JuanJ-S/DAFA/Imagenes/Diagramas/Bocetado, Sistema de Tuberias.jpeg

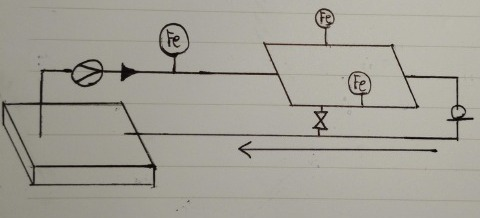
Imagenes/Diagramas/Bocetado, Sistema de Tuberias.jpeg
