JuanJ-S/DAFA/Imagenes/Diagramas/DAFA (ESP8266).png

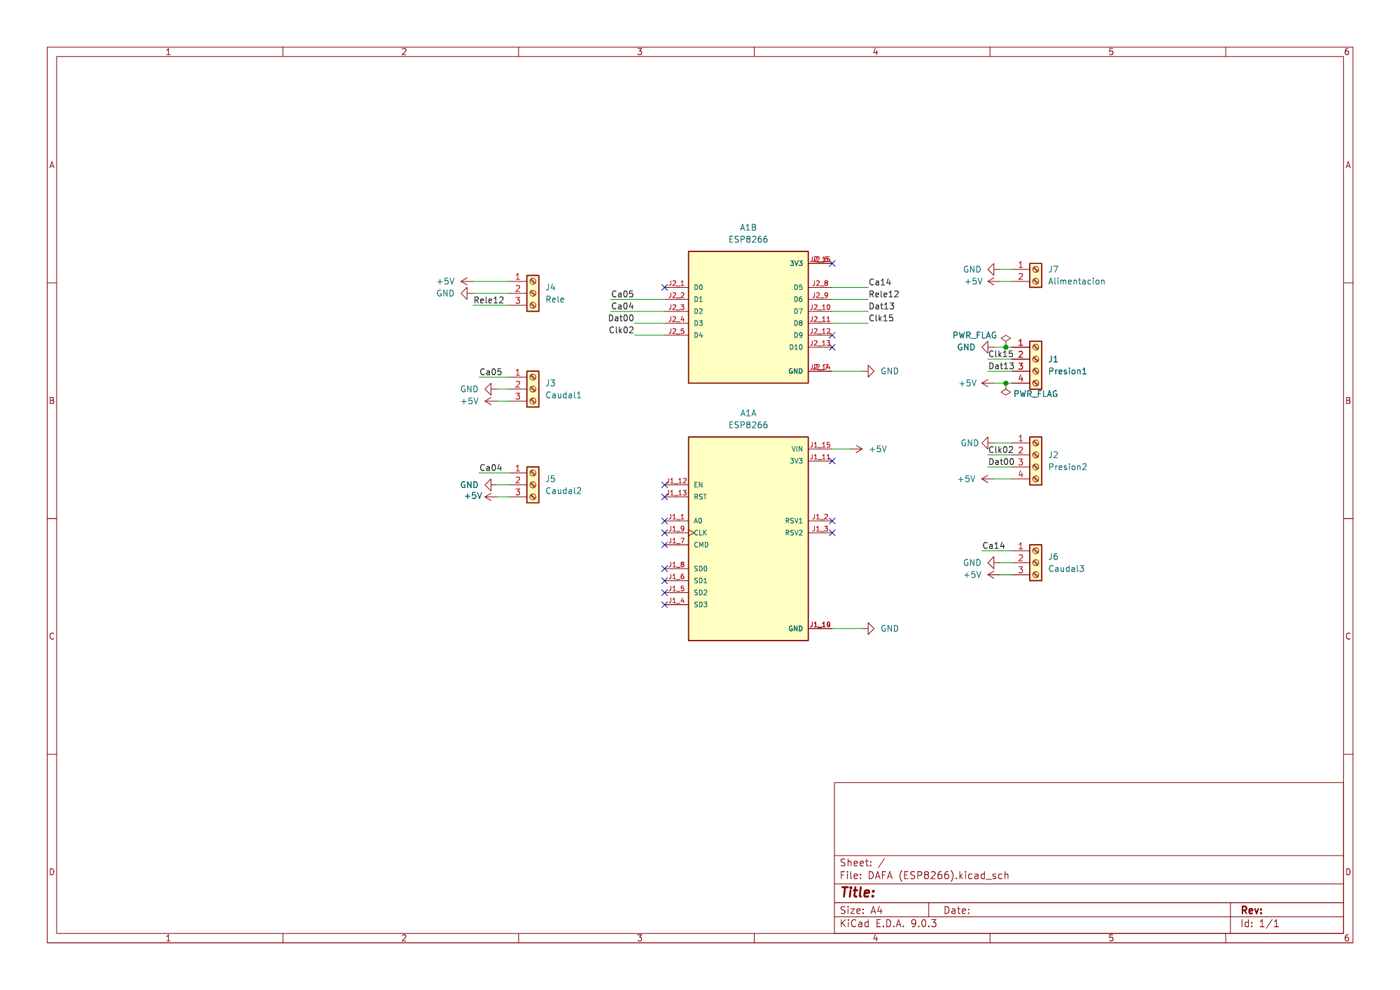
Imagenes/Diagramas/DAFA (ESP8266).png
