JuanJ-S/DAFA/Imagenes/Diagramas/Diagrama Funcionamiento.drawio.png

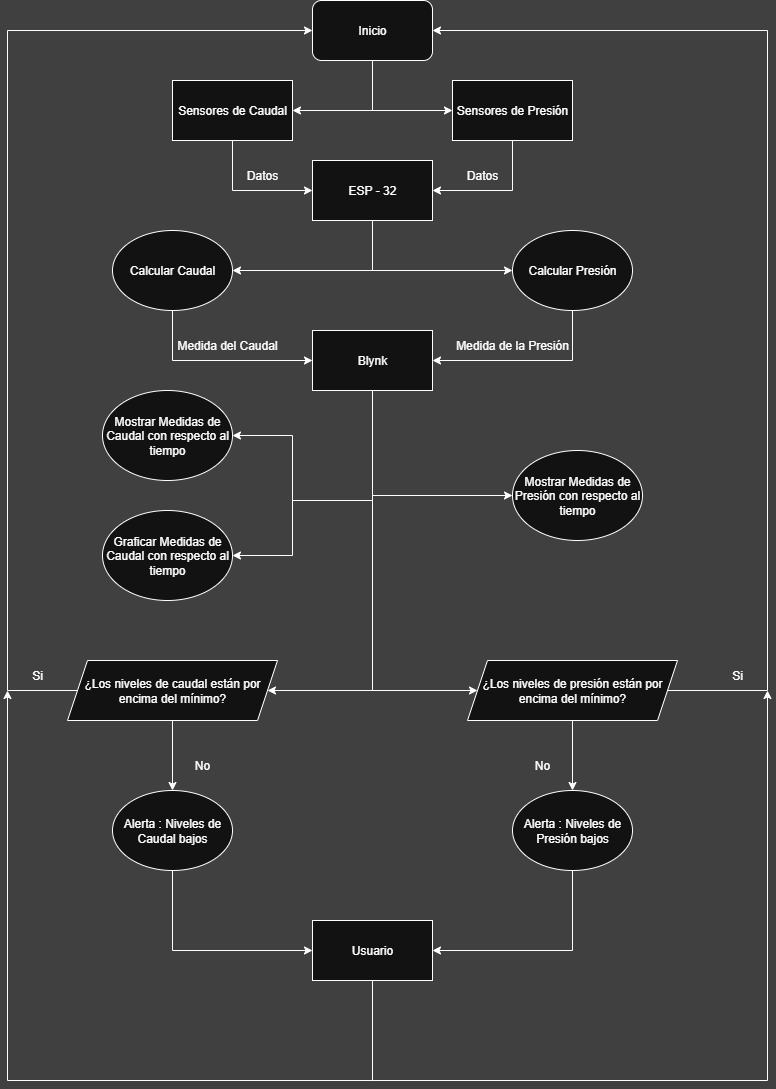
Imagenes/Diagramas/Diagrama Funcionamiento.drawio.png
