JuanJ-S/DAFA/Imagenes/Diagramas/Diagrama Tecnológico.png

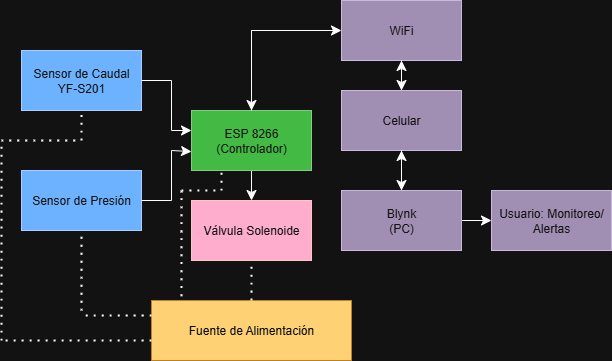
Imagenes/Diagramas/Diagrama Tecnológico.png
