JuanJ-S/DAFA/Imagenes/Diagramas/Esquema ESP32.jpeg

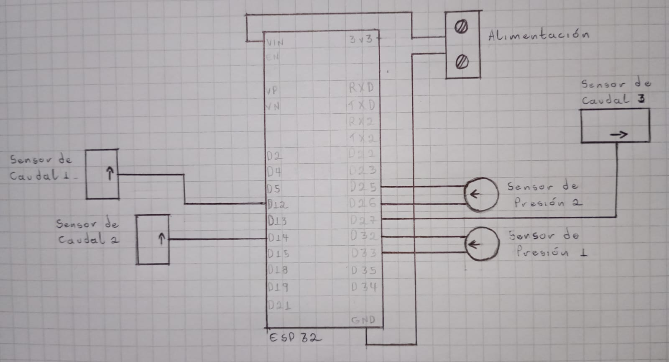
Imagenes/Diagramas/Esquema ESP32.jpeg
