JuanJ-S/DAFA/Imagenes/Diagramas/Interacción_usuario.drawio.png

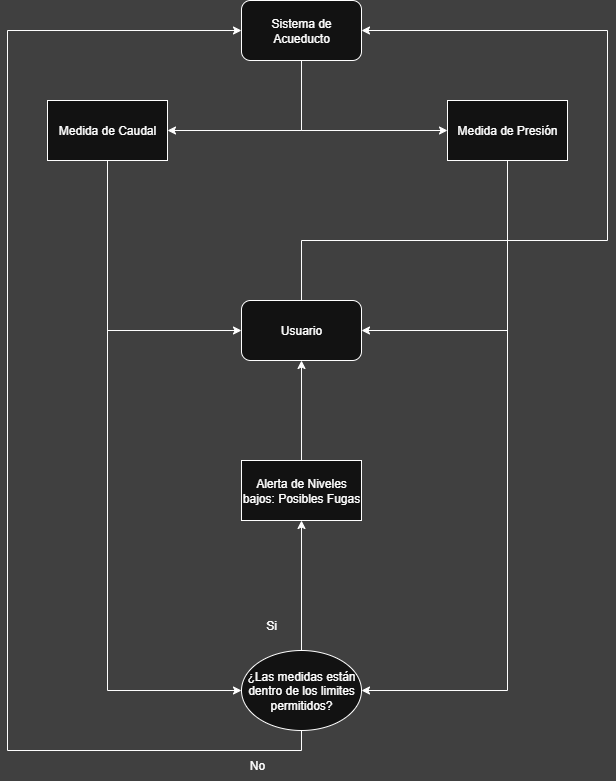
Imagenes/Diagramas/Interacción_usuario.drawio.png
