JuanJ-S/DAFA/Imagenes/Fotitos/Case - Inferior.png

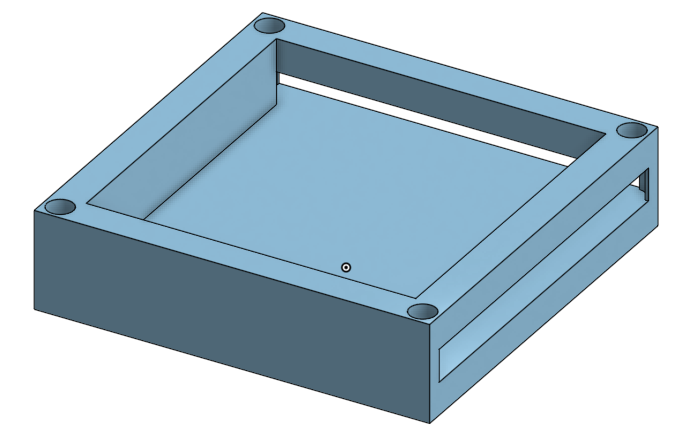
Imagenes/Fotitos/Case - Inferior.png
