JuanJ-S/DAFA/Imagenes/Fotitos/Case - Superior.png

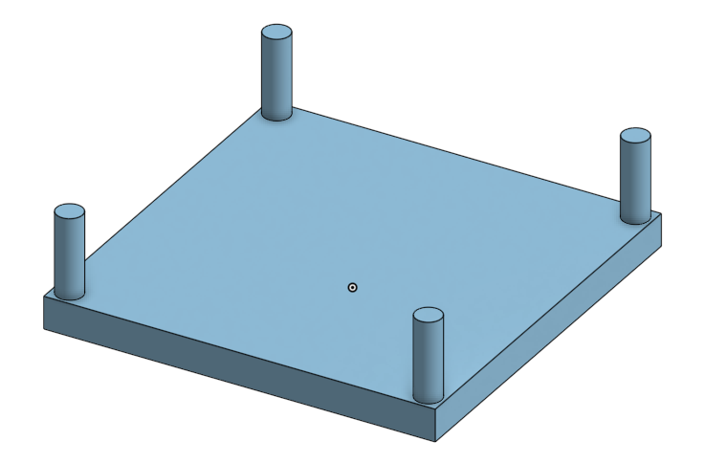
Imagenes/Fotitos/Case - Superior.png
