JuanJ-S/DAFA/Imagenes/Fotitos/Cronograma.jpg

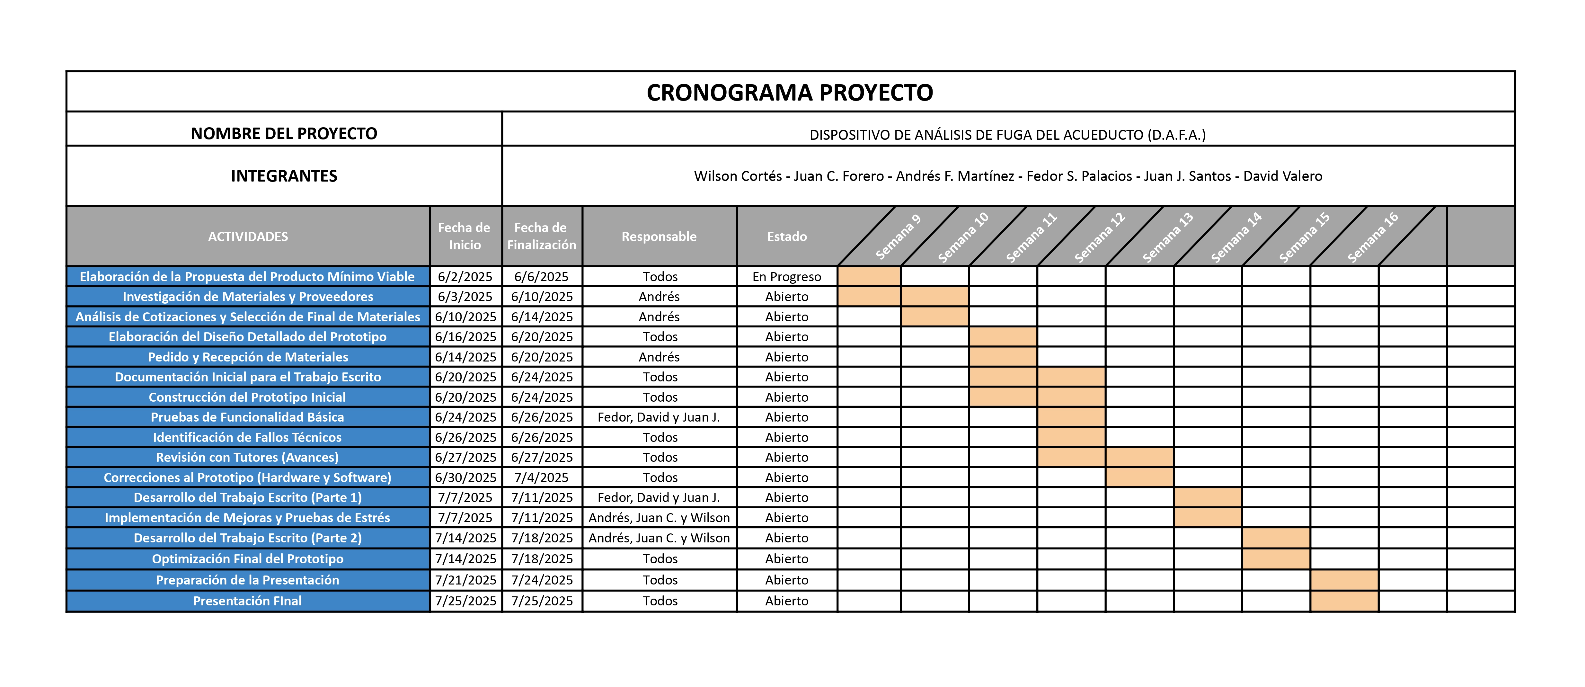
Imagenes/Fotitos/Cronograma.jpg
