JuanJ-S/DAFA/Imagenes/Fotitos/Evidencias/Datos - Antigua simulación.jpeg

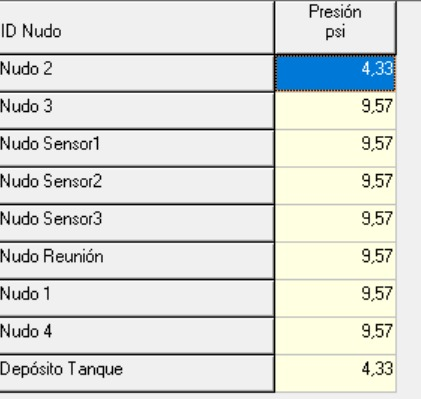
Imagenes/Fotitos/Evidencias/Datos - Antigua simulación.jpeg
