JuanJ-S/DAFA/Imagenes/Fotitos/Evidencias/PCB con tinta.jpeg

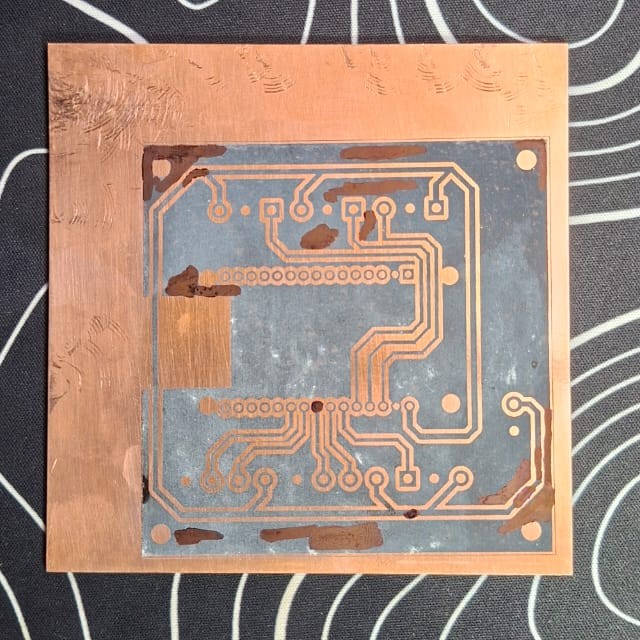
Imagenes/Fotitos/Evidencias/PCB con tinta.jpeg
