JuanJ-S/DAFA/Imagenes/Fotitos/Evidencias/PCB en Acido Ferrico.jpeg

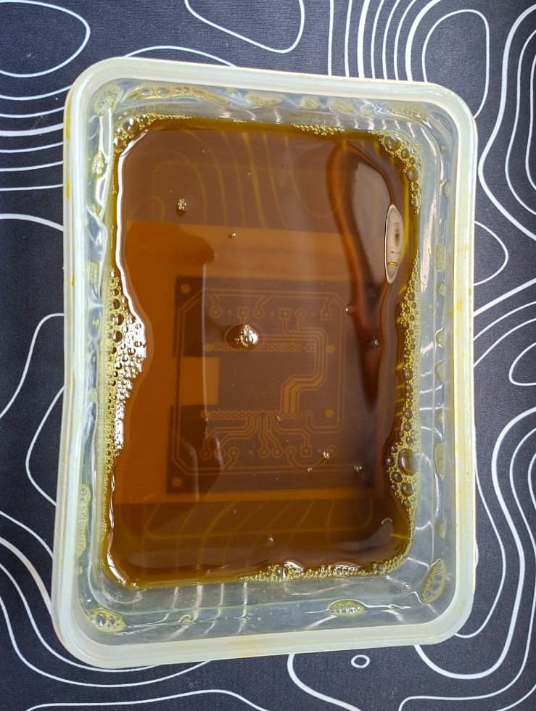
Imagenes/Fotitos/Evidencias/PCB en Acido Ferrico.jpeg
