JuanJ-S/DAFA/Imagenes/Fotitos/Evidencias/Post-Lijado.jpeg

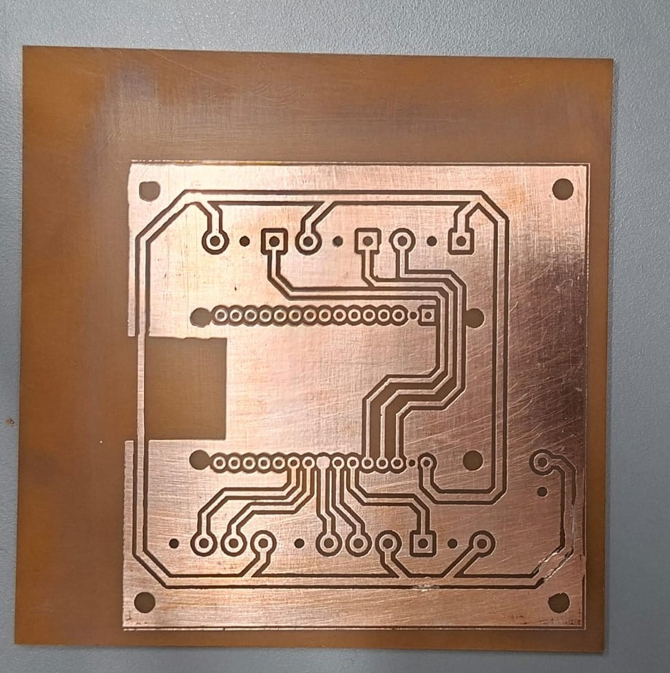
Imagenes/Fotitos/Evidencias/Post-Lijado.jpeg
