JuanJ-S/DAFA/Imagenes/Fotitos/Imagen PCB Layout.png

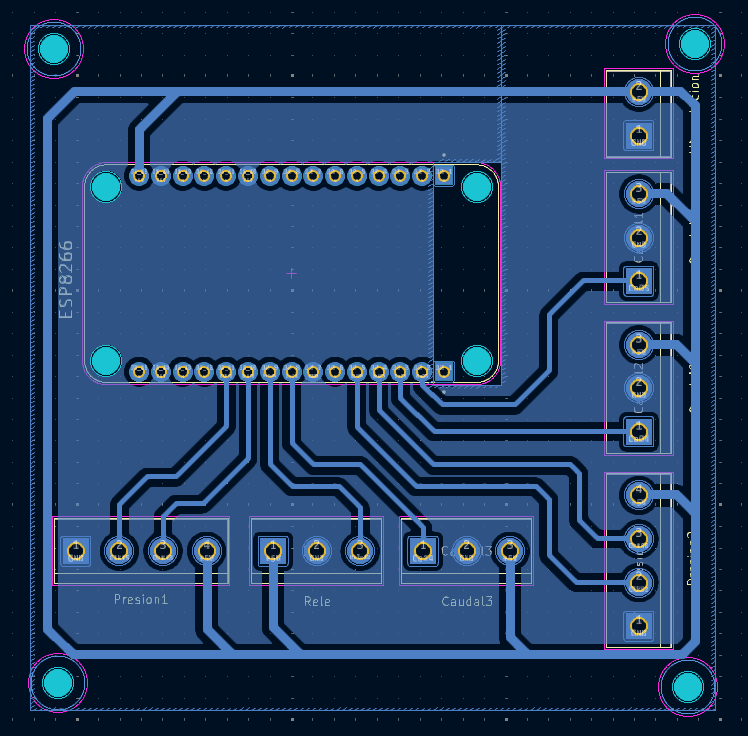
Imagenes/Fotitos/Imagen PCB Layout.png
