JuanJ-S/DAFA/Imagenes/Fotitos/Ensamble.png

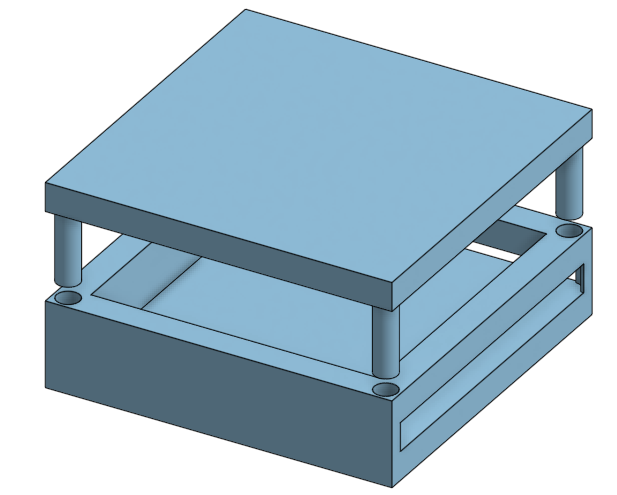
Imagenes/Fotitos/Ensamble.png
