JuanJ-S/DAFA/Imagenes/Fotitos/Evidencias/Prueba - Sensores de Caudal.jpeg

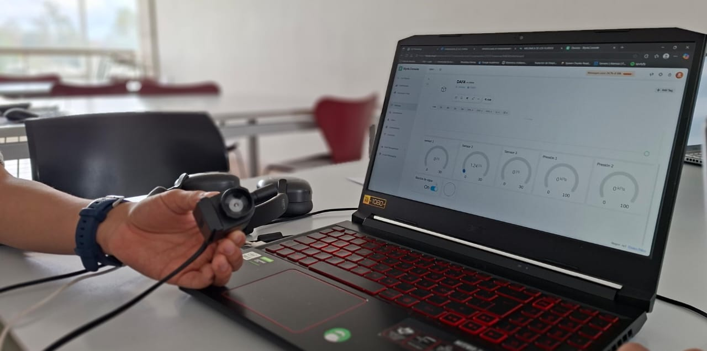
Imagenes/Fotitos/Evidencias/Prueba - Sensores de Caudal.jpeg
