JuanJ-S/DAFA/Imagenes/Fotitos/Evidencias/Prueba de Sensores.jpeg

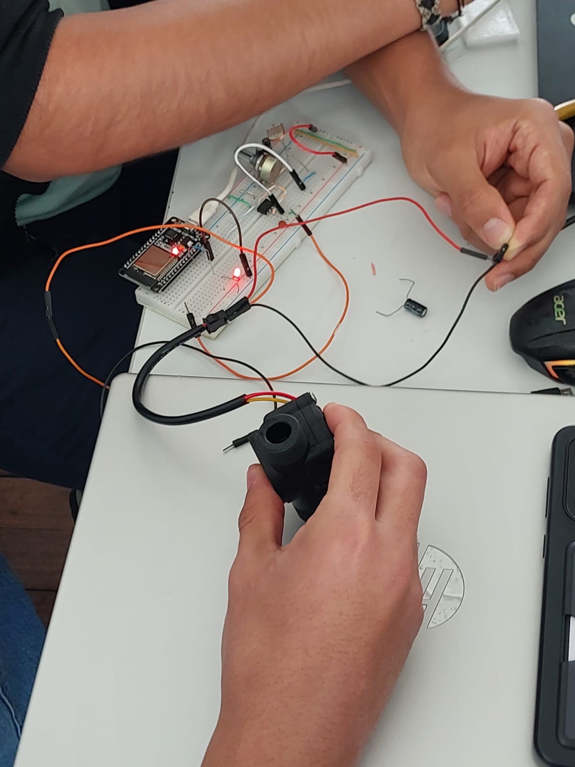
Imagenes/Fotitos/Evidencias/Prueba de Sensores.jpeg
